errsu/opendigitalmodular/documentation/images/analog_synth_structure.png

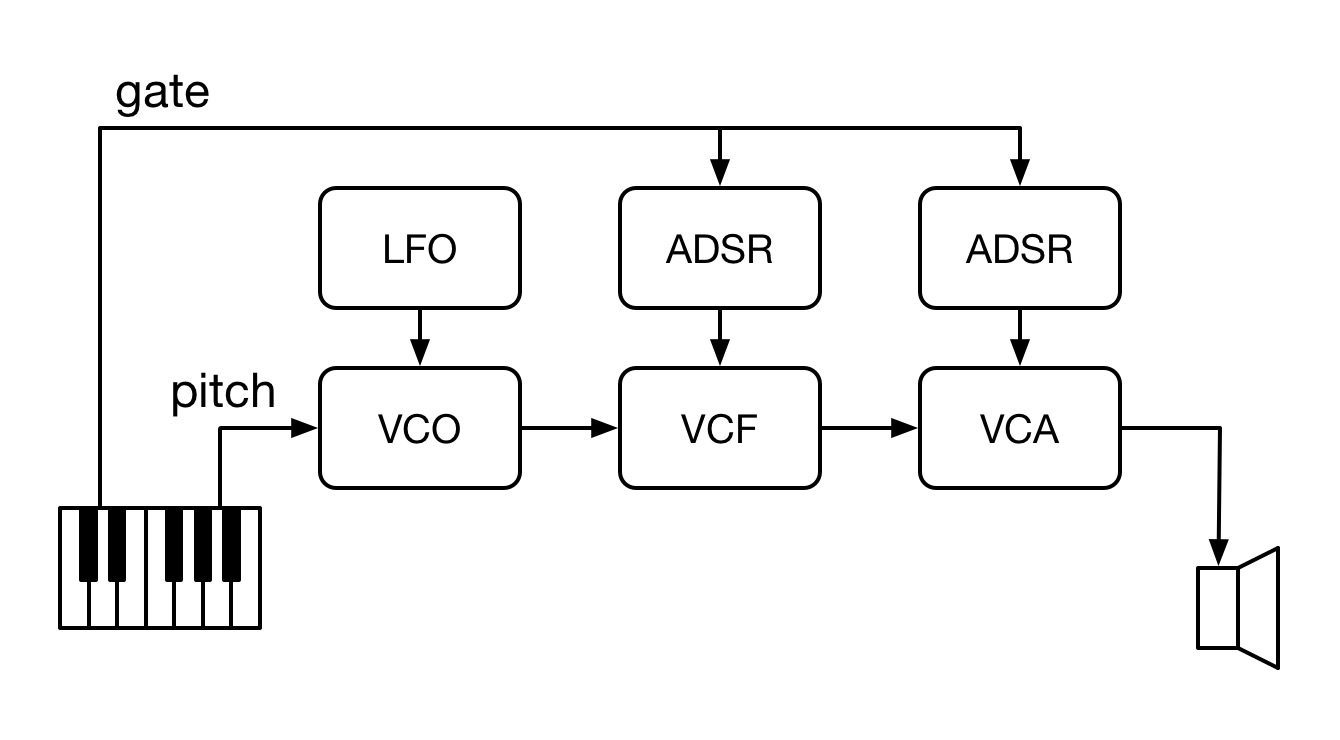
documentation/images/analog_synth_structure.png
