errsu/opendigitalmodular/documentation/images/diagnostic_module.png

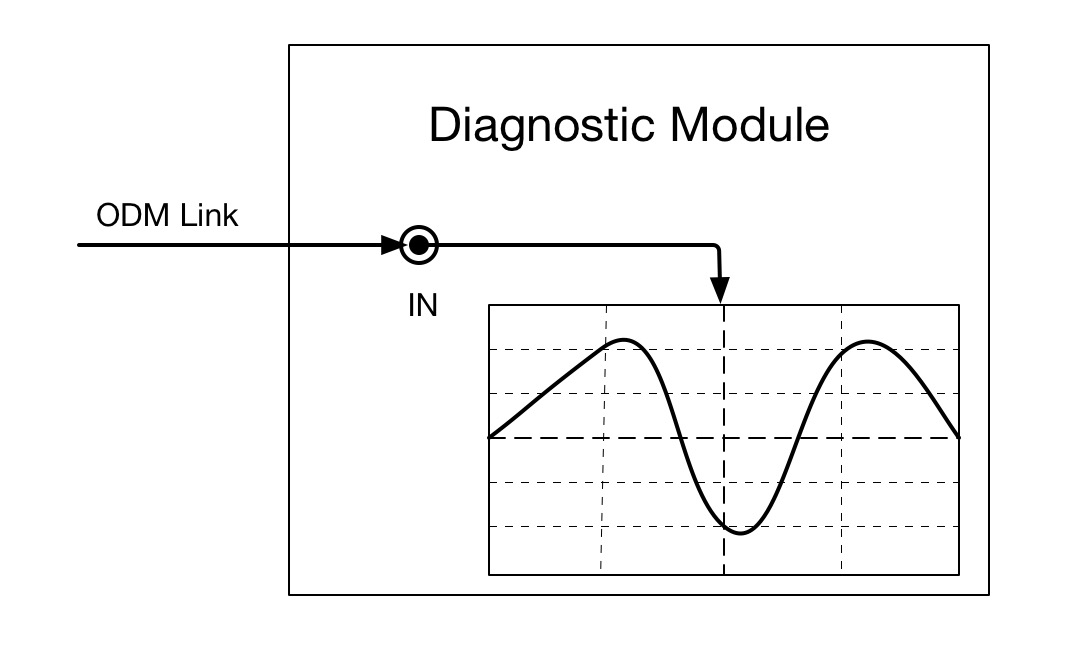
documentation/images/diagnostic_module.png
