errsu/opendigitalmodular/documentation/images/internal_module_structure.png

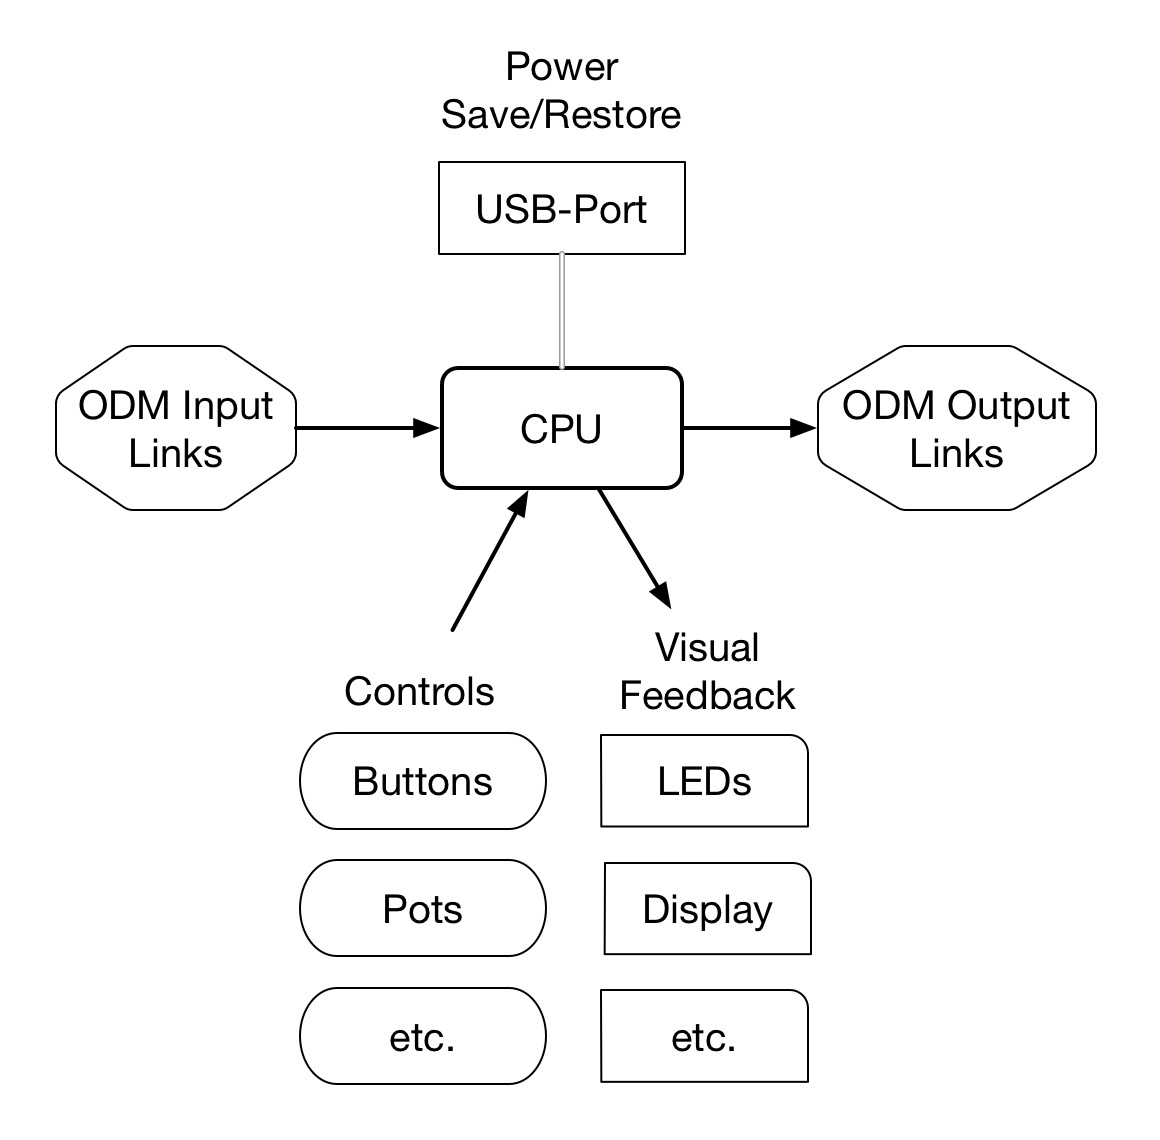
documentation/images/internal_module_structure.png
