errsu/opendigitalmodular/documentation/images/odm_dm_veroboard.png

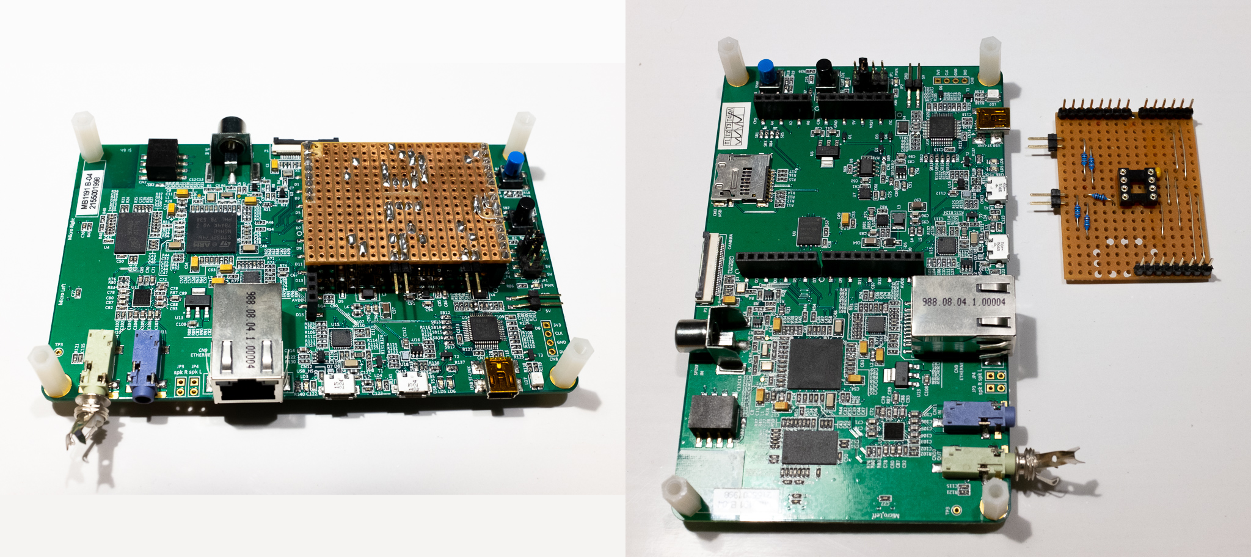
documentation/images/odm_dm_veroboard.png
