errsu/opendigitalmodular/documentation/images/odm_link.png

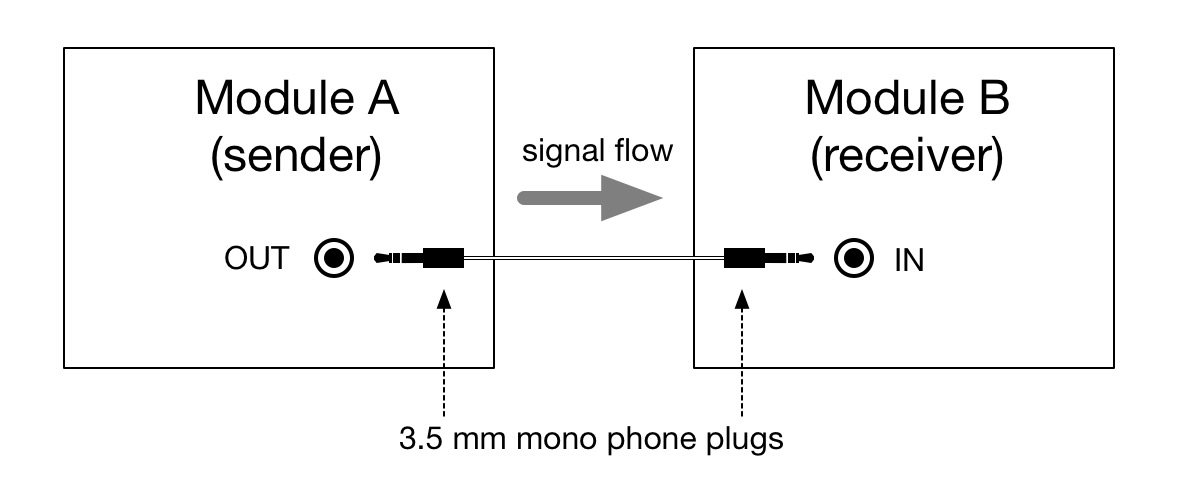
documentation/images/odm_link.png
