errsu/opendigitalmodular/documentation/images/odm_link_physical_layer.png

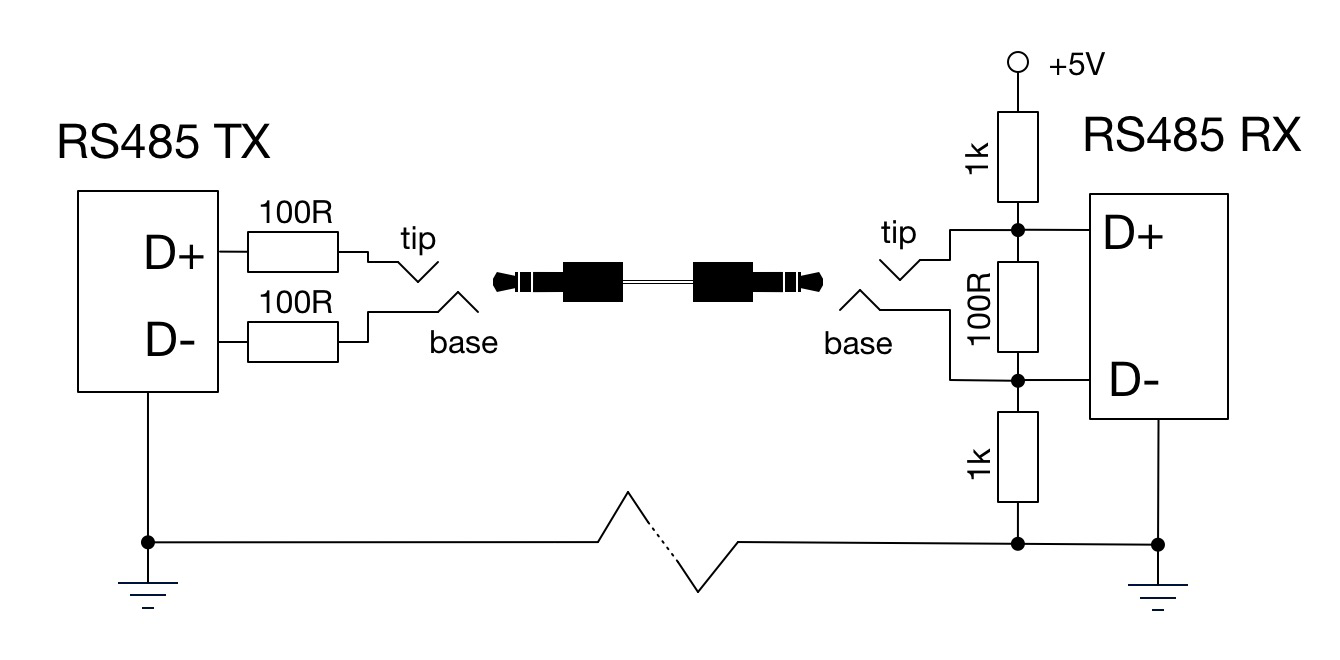
documentation/images/odm_link_physical_layer.png
