errsu/opendigitalmodular/documentation/images/odm_link_protocol.png

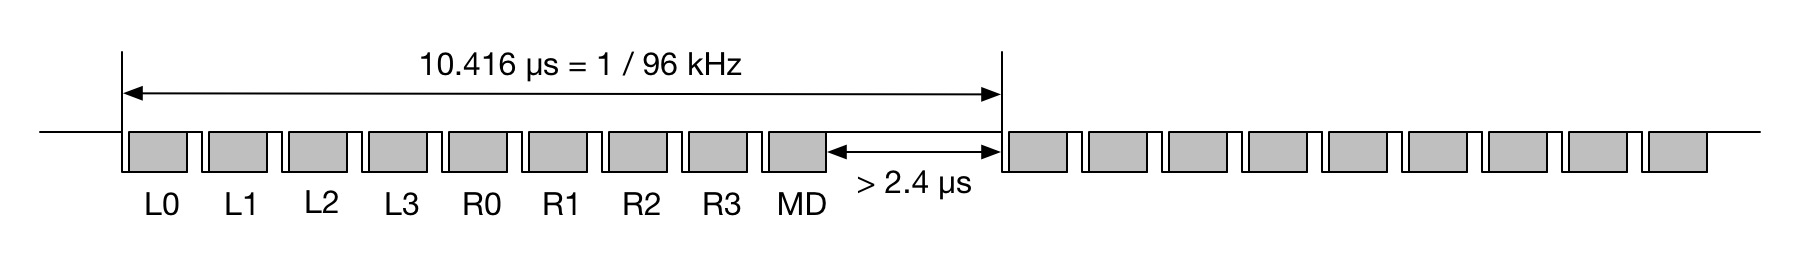
documentation/images/odm_link_protocol.png
