errsu/opendigitalmodular/documentation/images/odm_synth_structure.png

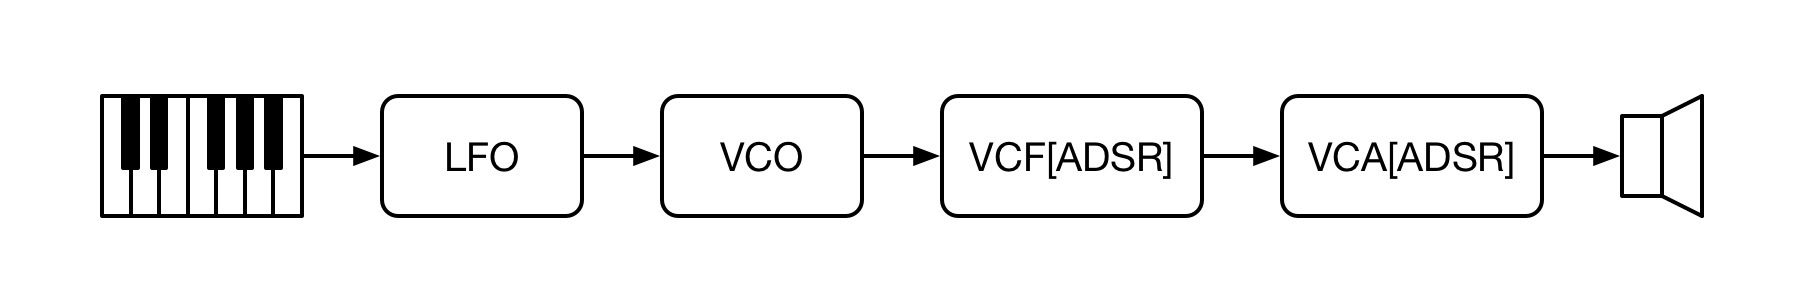
documentation/images/odm_synth_structure.png
