errsu/opendigitalmodular/documentation/images/one_to_many.png

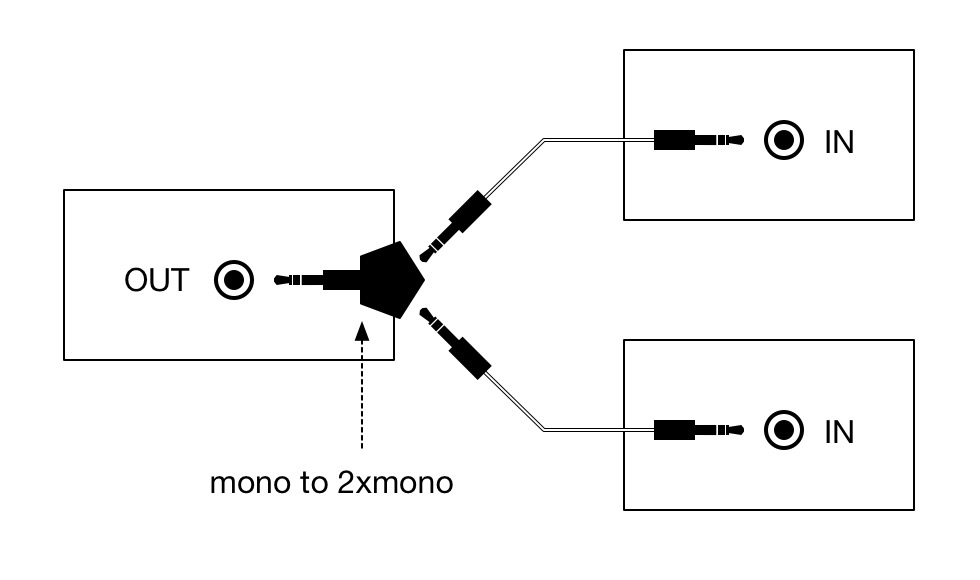
documentation/images/one_to_many.png
