errsu/opendigitalmodular/documentation/images/power_supply.png

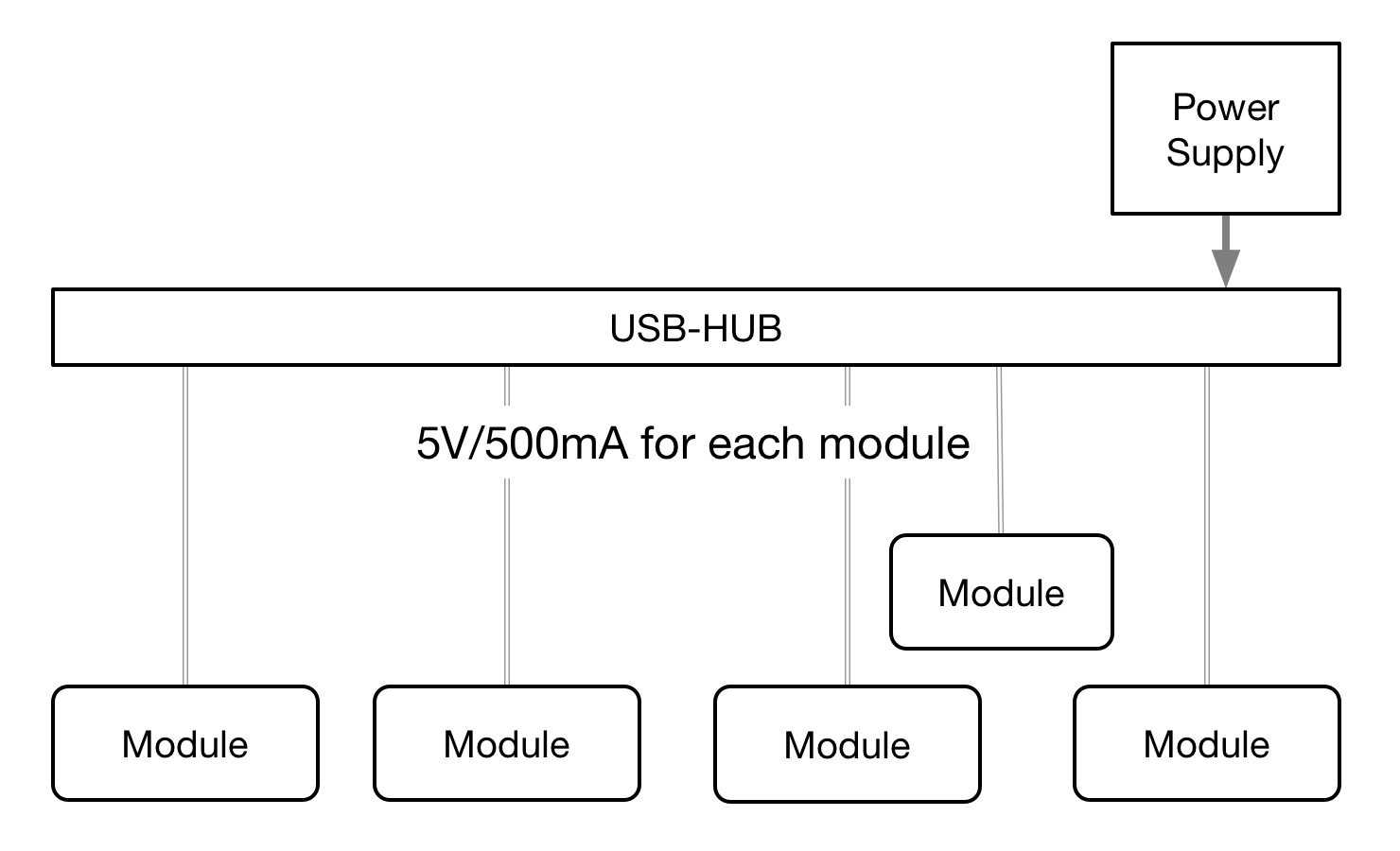
documentation/images/power_supply.png
