errsu/opendigitalmodular/documentation/images/pure_usb_io.png

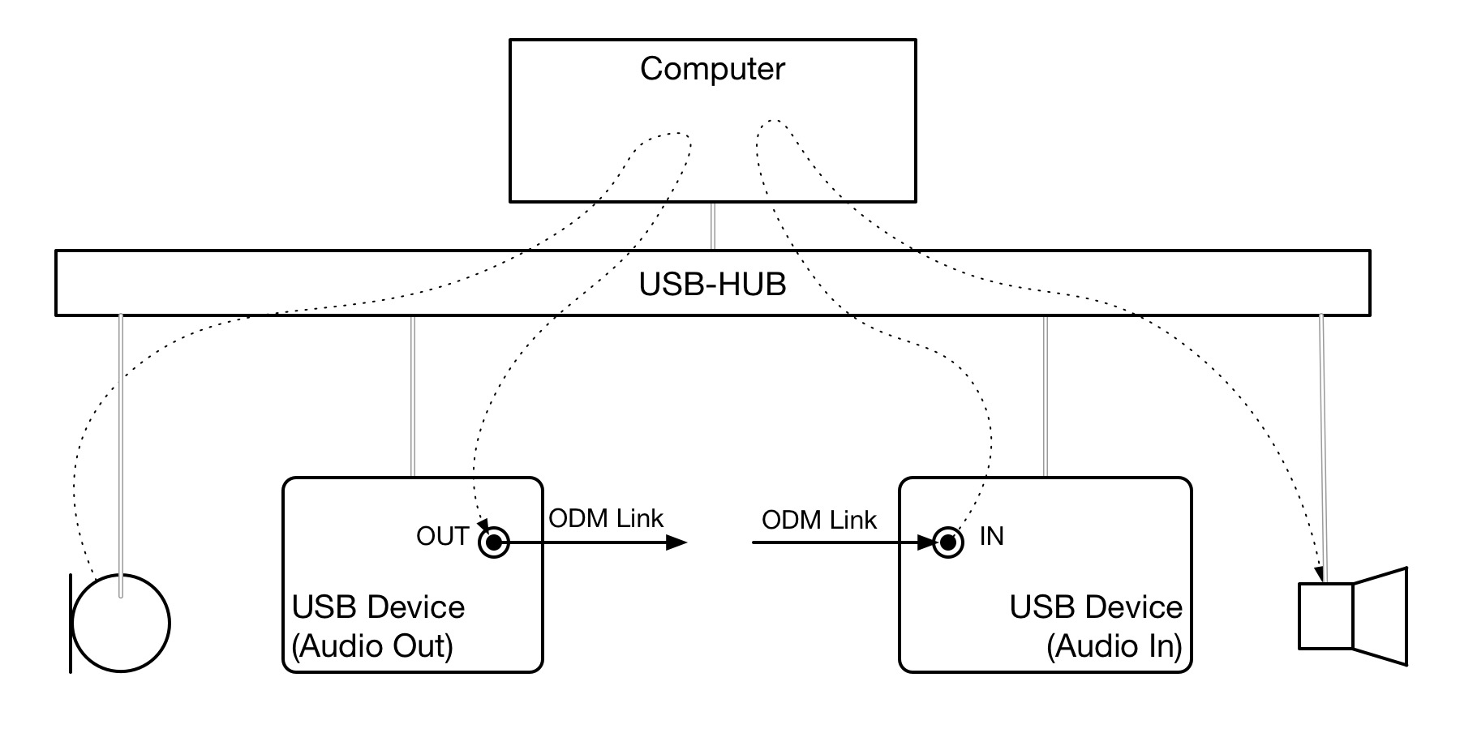
documentation/images/pure_usb_io.png
