errsu/opendigitalmodular/documentation/images/save_restore.png

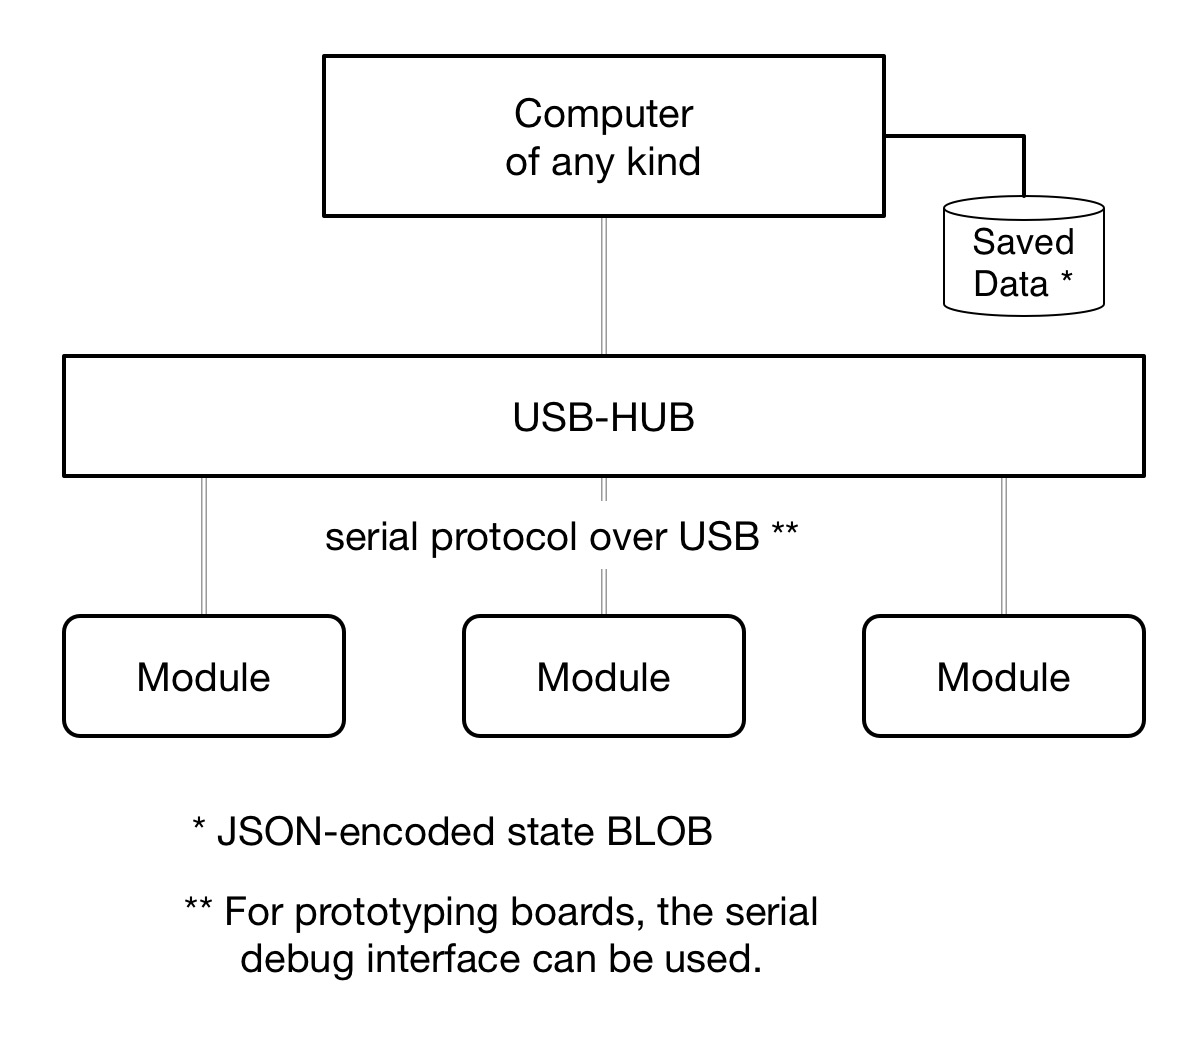
documentation/images/save_restore.png
