errsu/opendigitalmodular/documentation/images/sync_via_midi.png

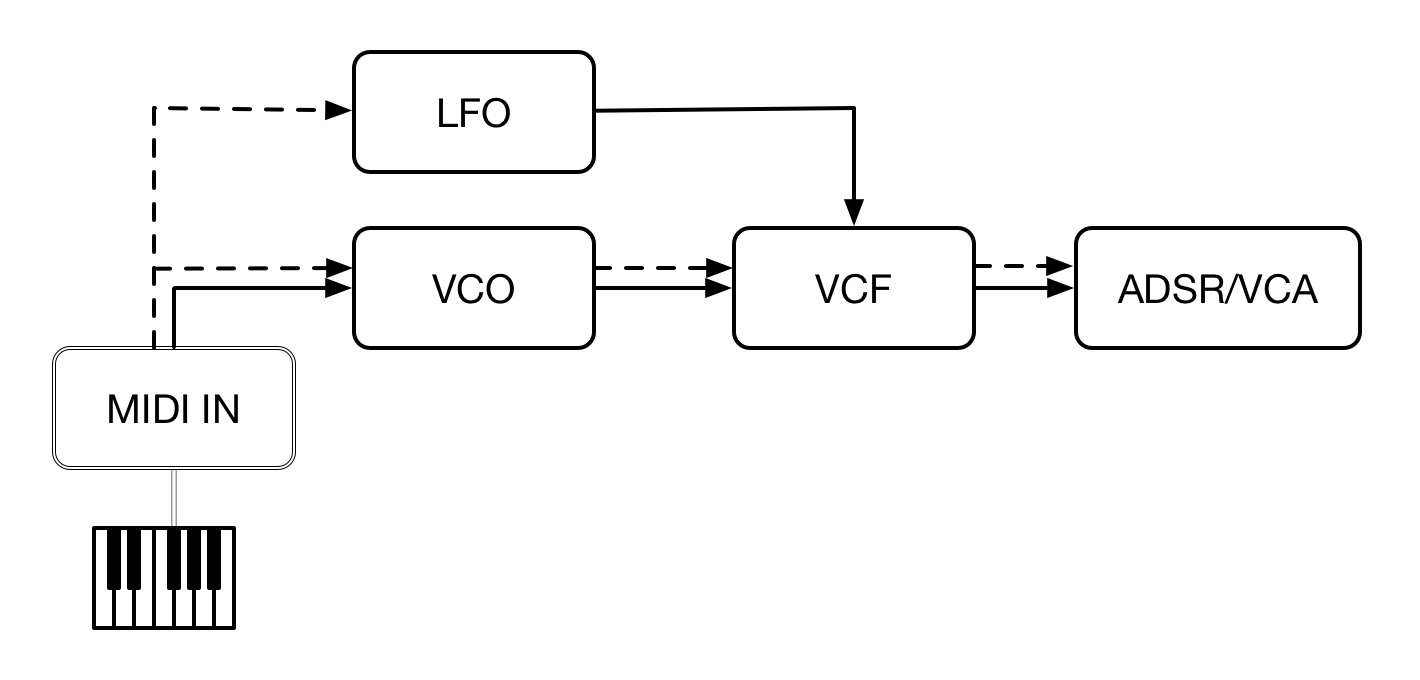
documentation/images/sync_via_midi.png
