errsu/opendigitalmodular/documentation/images/usb_audio_io.png

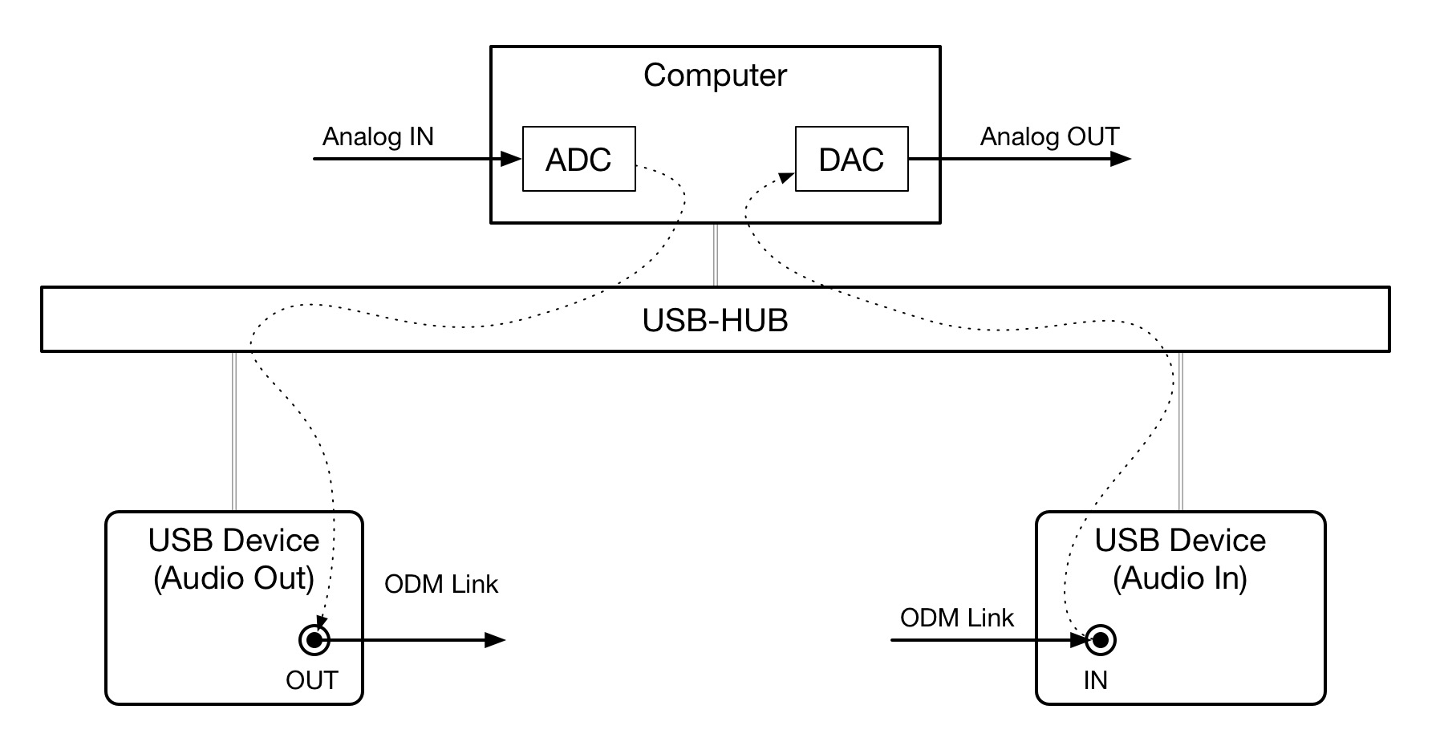
documentation/images/usb_audio_io.png
